achillecalegari/calegari-view-2/docs/img/02_front.jpg

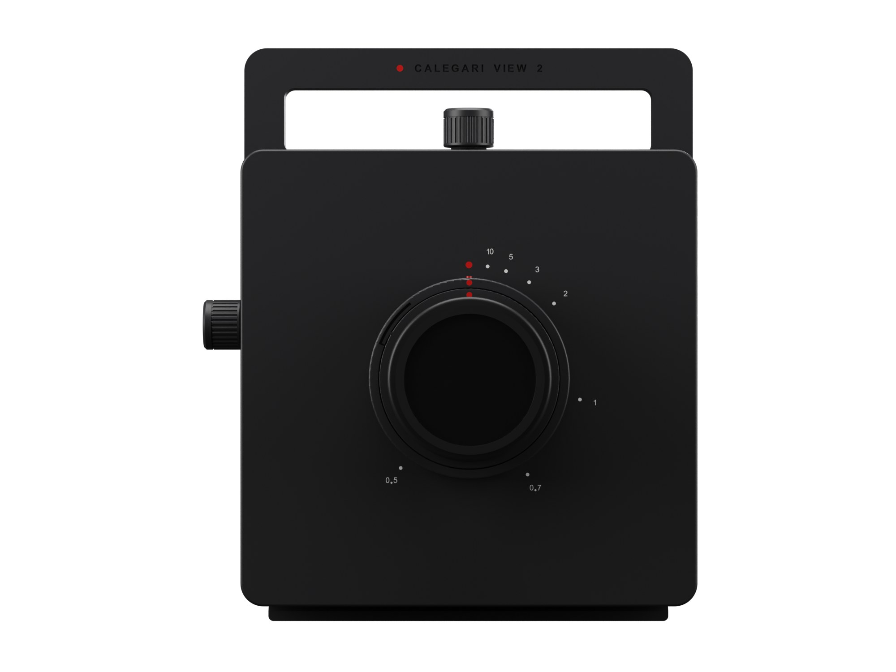
docs/img/02_front.jpg
