achillecalegari/calegari-view-2/docs/img/05_top.jpg

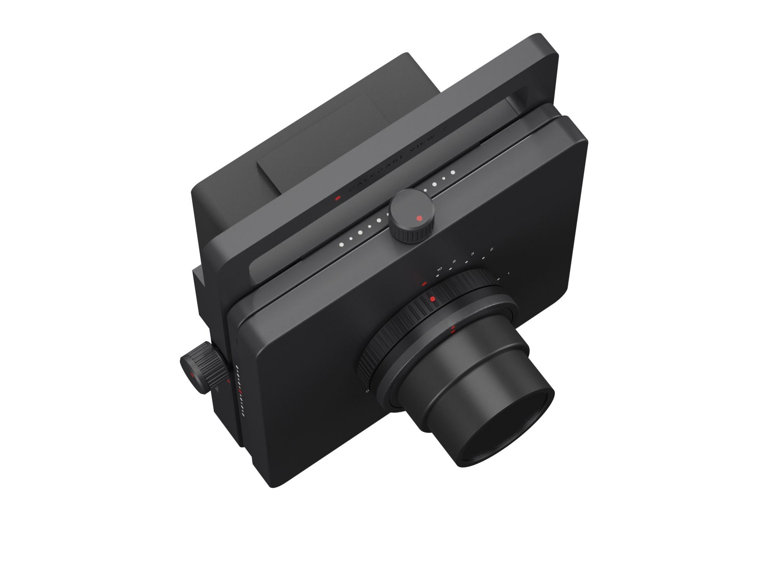
docs/img/05_top.jpg
