achillecalegari/calegari-view-2/print/plates/plate_00d_test_tpu.3mf

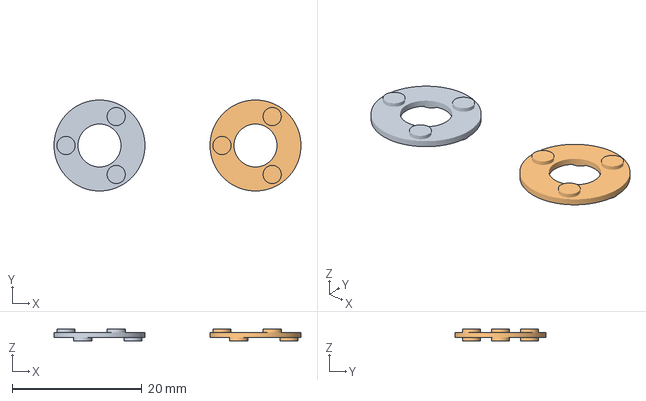
[picture p22: CAD file, 2026-09-29]
print/plates/plate_00d_test_tpu.3mf
38.0 x 14.0 x 1.80 mm
tpu_drag_washer
tpu_drag_washer_b
