achillecalegari/calegari-view-2/print/step/plug_x_bottom.step

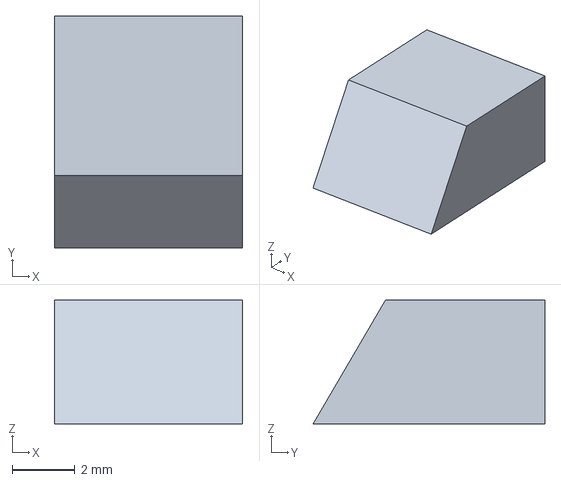
[picture p23: CAD file, 2026-09-29]
print/step/plug_x_bottom.step
6.01 x 7.41 x 3.95 mm
