achillecalegari/calegari-view-2/print/test/worm_rig_plug.stl

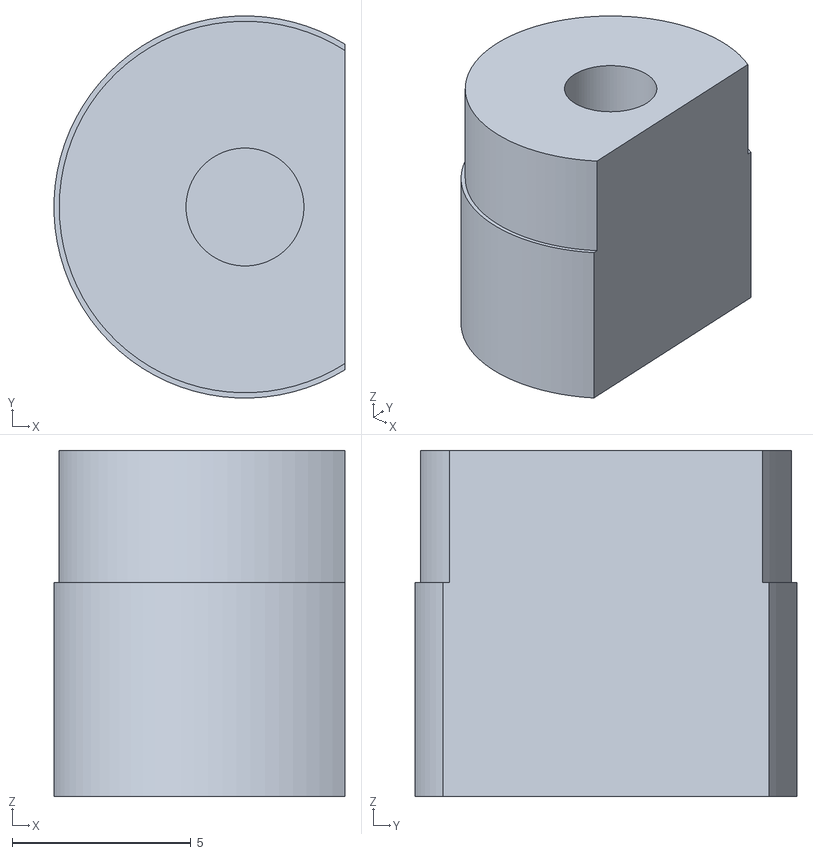
[picture p24: CAD file, 2026-09-28]
print/test/worm_rig_plug.stl
8.15 x 10.7 x 9.70
