achillecalegari/calegari-view-2/print/plates/plate_00c_test_ways_arca.3mf

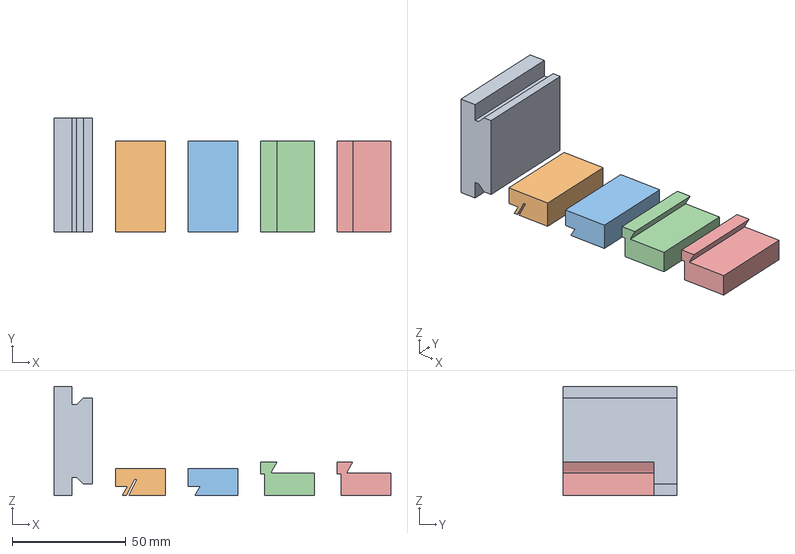
[picture p25: CAD file, 2026-09-29]
print/plates/plate_00c_test_ways_arca.3mf
148.4 x 50.0 x 48.0 mm
arca_coupon
way_groove_flexure
way_groove_rigid
way_tongue_flexure
way_tongue_rigid
