achillecalegari/calegari-view-2/print/test/collar.stl

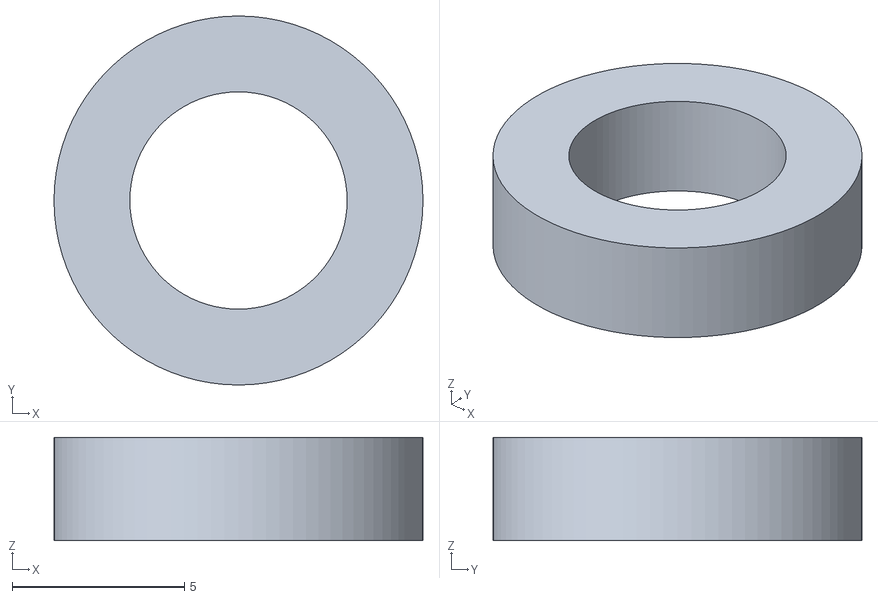
[picture p26: CAD file, 2026-09-28]
print/test/collar.stl
10.7 x 10.7 x 3.00
