achillecalegari/calegari-view-2/print/plates/plate_04_black_0.12mm_layers.3mf

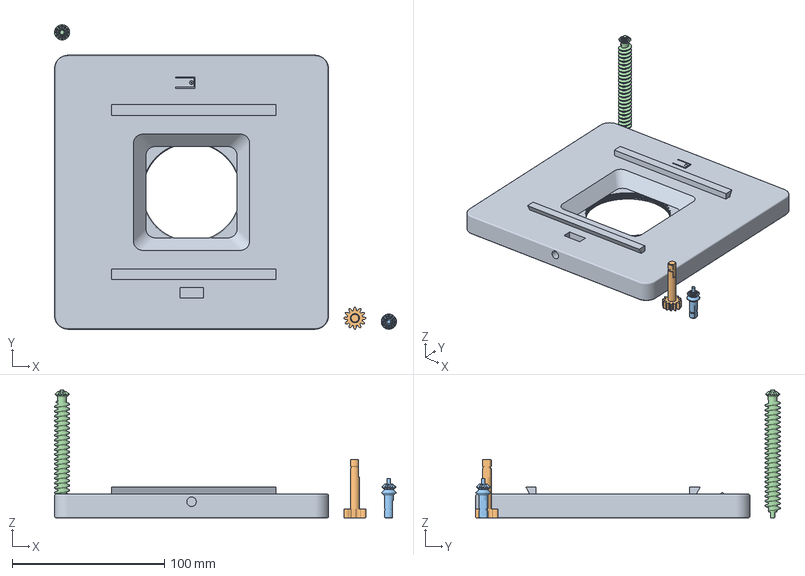
[picture p27: CAD file, 2026-09-29]
print/plates/plate_04_black_0.12mm_layers.3mf
224.6 x 200.0 x 83.9 mm
lens_panel
pinion_shift
rise_knob_gear
rise_worm
