achillecalegari/calegari-view-2/print/step/plug_worm.step

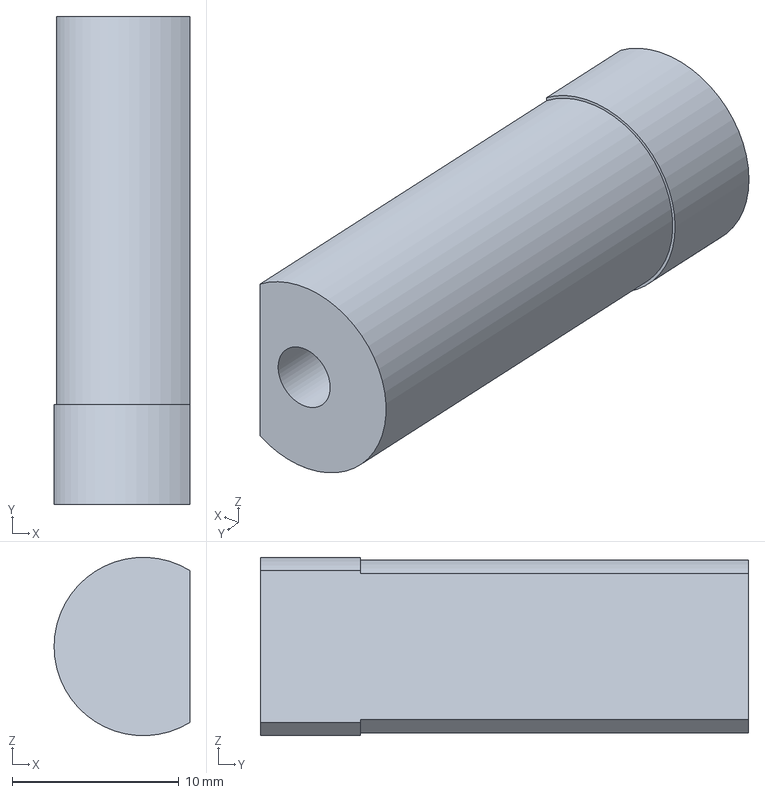
[picture p28: CAD file, 2026-09-29]
print/step/plug_worm.step
8.15 x 29.3 x 10.7 mm
