achillecalegari/calegari-view-2/print/test/pinion_shaft.stl

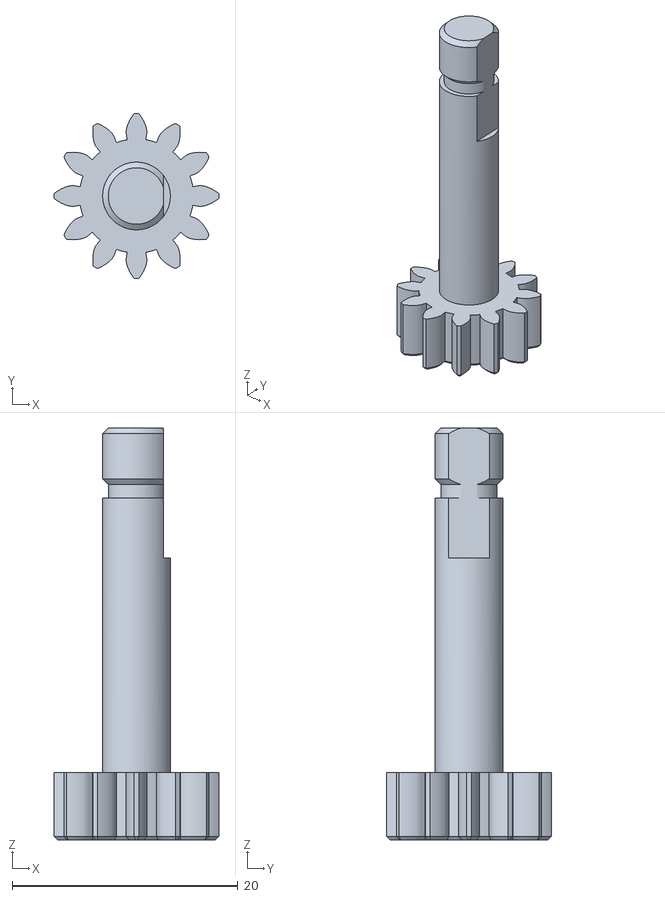
[picture p29: CAD file, 2026-09-28]
print/test/pinion_shaft.stl
14.6 x 14.6 x 36.5
