achillecalegari/calegari-view-2/print/plates/plate_02_black.3mf

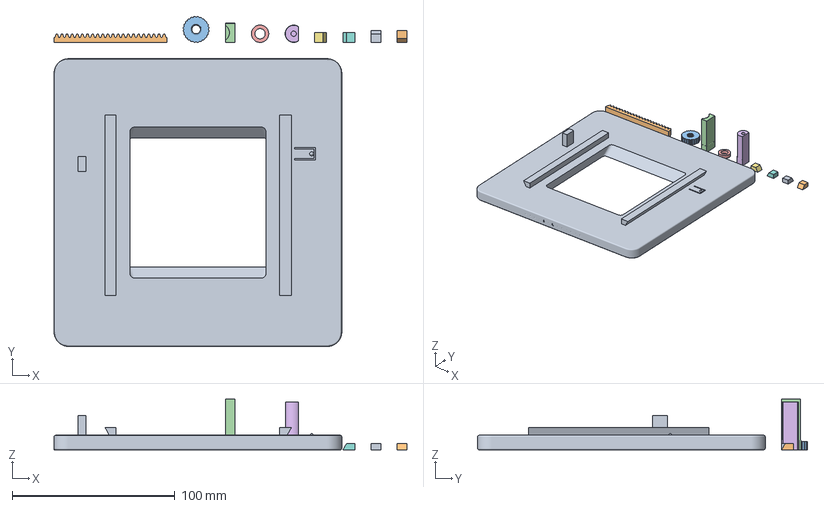
[picture p30: CAD file, 2026-09-29]
print/plates/plate_02_black.3mf
217.1 x 203.0 x 31.2 mm
y_plate
rack_shift
graflok_wheel
plug_rack
rise_collar
plug_worm
plug_y_left
plug_y_right
plug_x_top
plug_x_bottom
