achillecalegari/calegari-view-2/print/step/y_plate.step

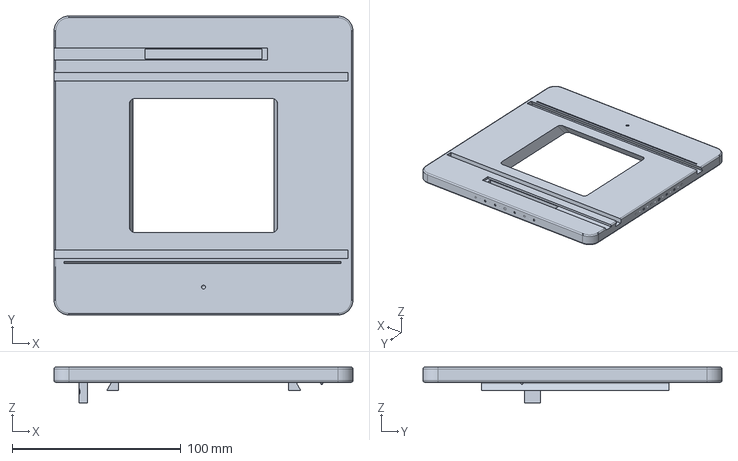
[picture p31: CAD file, 2026-09-29]
print/step/y_plate.step
177.0 x 177.0 x 21.2 mm
