achillecalegari/calegari-view-2/print/step/graflok_wheel.step

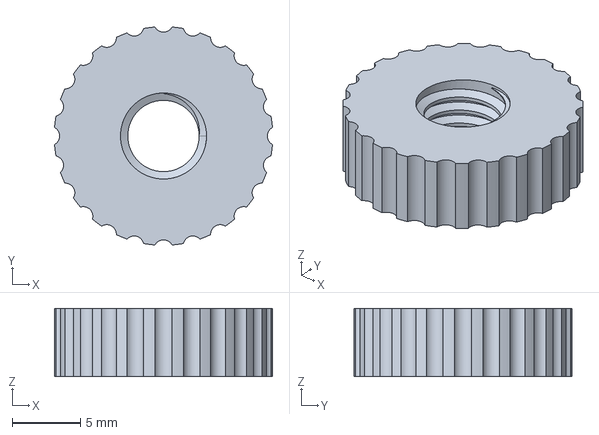
[picture p32: CAD file, 2026-09-29]
print/step/graflok_wheel.step
16.0 x 16.0 x 5.00 mm
