achillecalegari/calegari-view-2/print/test/rack_62.stl

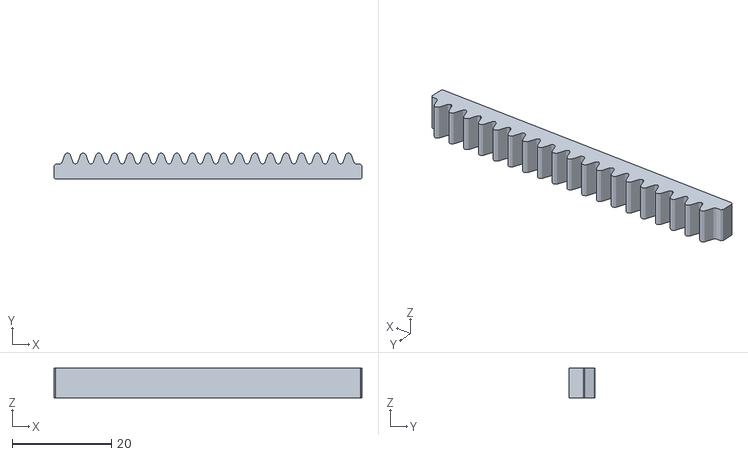
[picture p33: CAD file, 2026-09-28]
print/test/rack_62.stl
62.0 x 5.25 x 6.00
