achillecalegari/calegari-view-2/print/plates/plate_00b_test_lens_drive.3mf

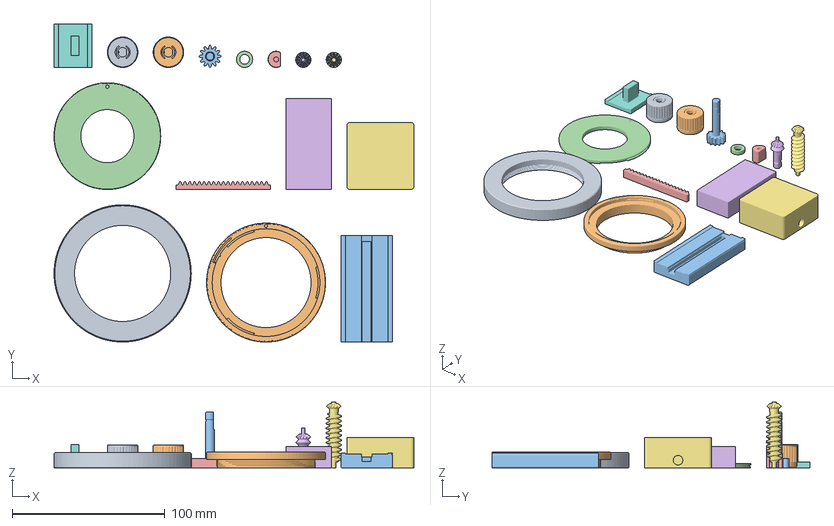
[picture p34: CAD file, 2026-09-29]
print/plates/plate_00b_test_lens_drive.3mf
236.0 x 208.6 x 43.1 mm
thread_coupon_M65_female
lens_mount
rack_carrier
lens_board
rack_62
worm_block
pinion_block
rise_rack_slice
knob
knob_b
pinion_shaft
collar
worm_rig_plug
knob_gear
worm_short
