achillecalegari/calegari-view-2/print/step/lens_panel.step

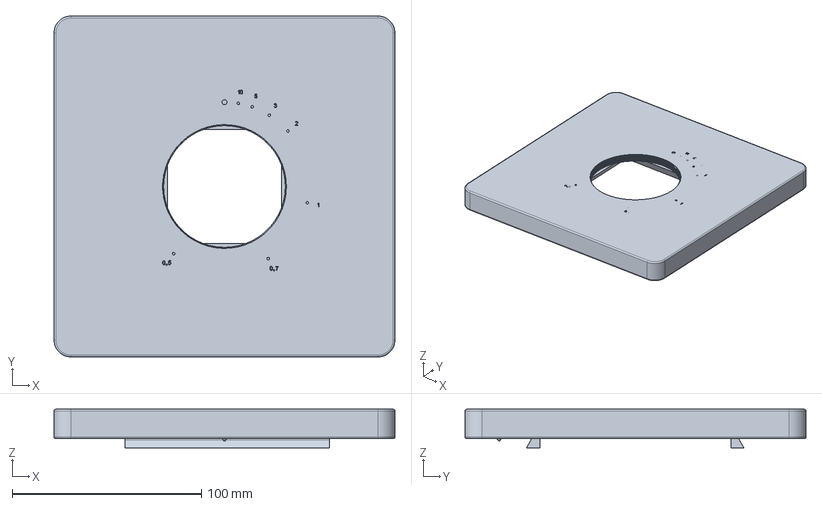
[picture p35: CAD file, 2026-09-29]
print/step/lens_panel.step
180.0 x 180.0 x 20.4 mm
