achillecalegari/calegari-view-2/print/test/thread_coupon_M65_female.stl

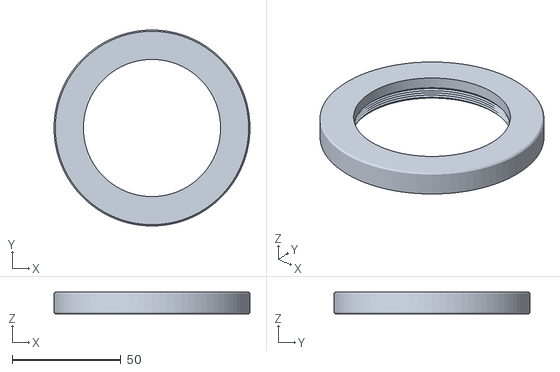
[picture p36: CAD file, 2026-09-28]
print/test/thread_coupon_M65_female.stl
90.0 x 90.0 x 10.0
