achillecalegari/calegari-view-2/print/test/arca_coupon.stl

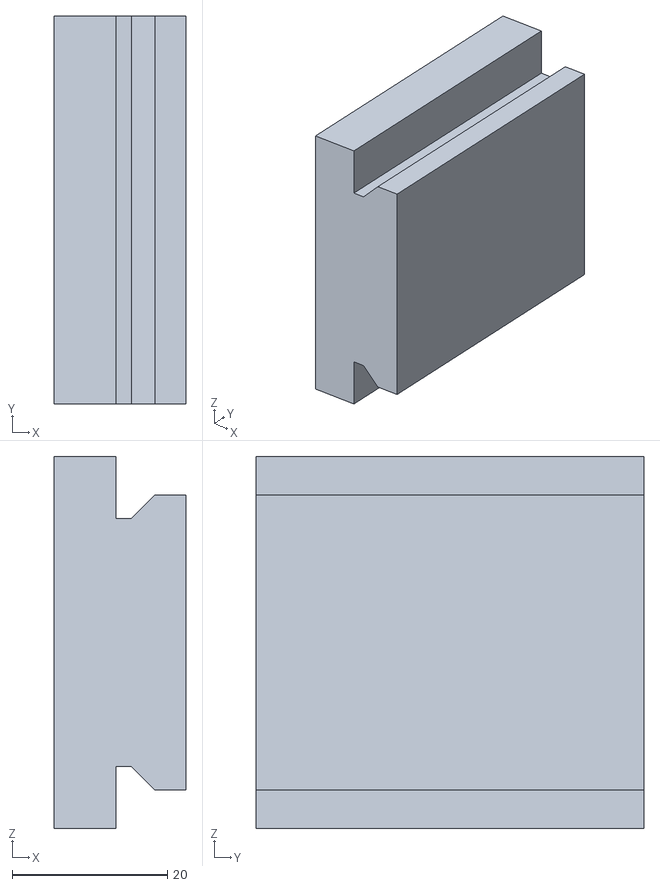
[picture p37: CAD file, 2026-09-28]
print/test/arca_coupon.stl
17.0 x 50.0 x 48.0
