achillecalegari/calegari-view-2/print/test/way_tongue_rigid.stl

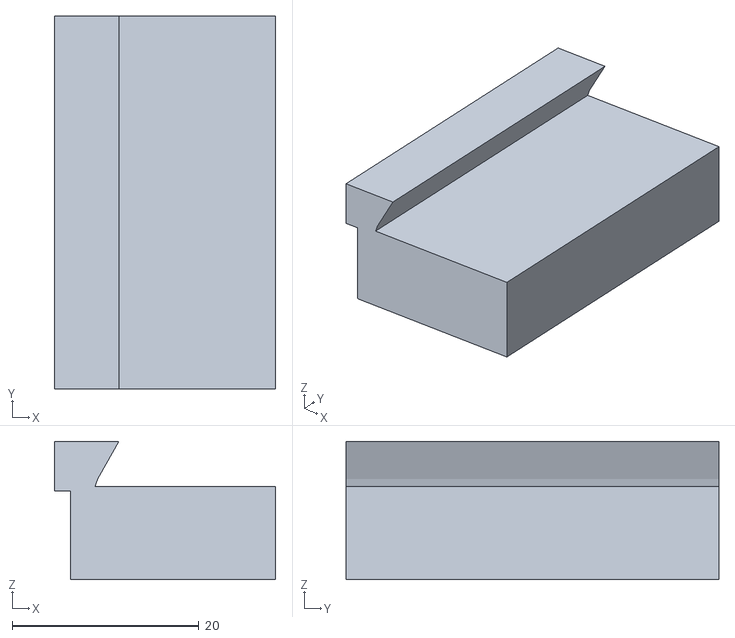
[picture p38: CAD file, 2026-09-28]
print/test/way_tongue_rigid.stl
23.7 x 40.0 x 14.8
