achillecalegari/calegari-view-2/print/step/pinion_shift.step

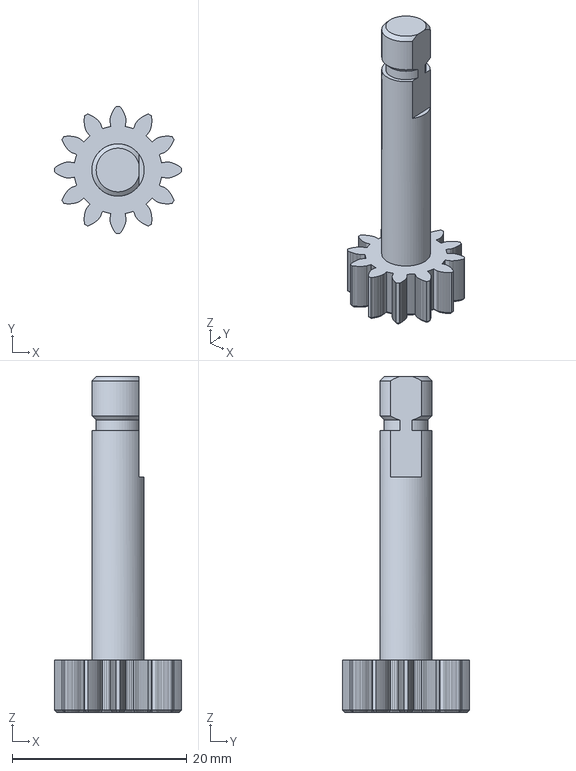
[picture p39: CAD file, 2026-09-29]
print/step/pinion_shift.step
14.6 x 14.6 x 38.5 mm
