achillecalegari/calegari-view-2/print/step/rise_worm.step

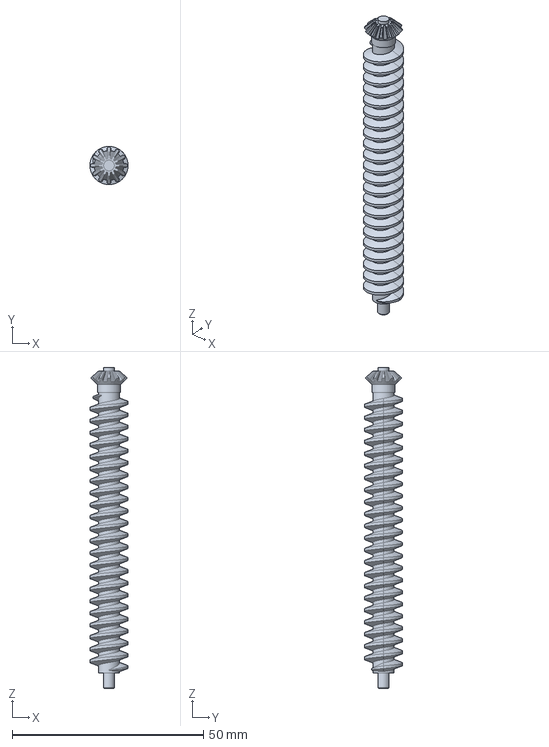
[picture p40: CAD file, 2026-09-29]
print/step/rise_worm.step
10.00 x 10.00 x 83.9 mm
