achillecalegari/calegari-view-2/print/test/way_groove_flexure.stl

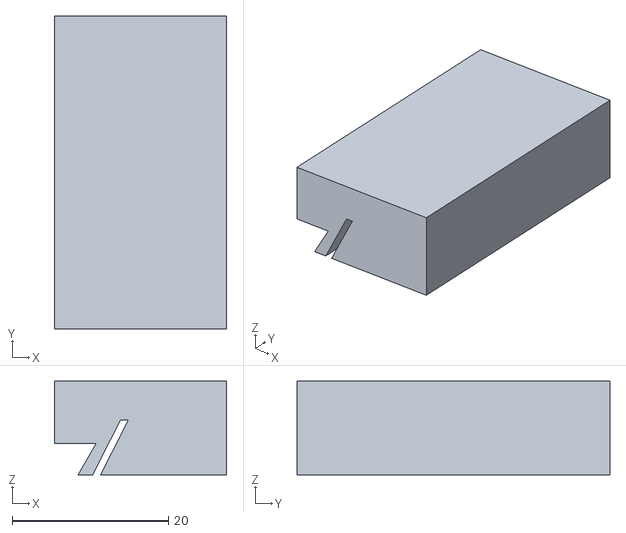
[picture p41: CAD file, 2026-09-28]
print/test/way_groove_flexure.stl
22.0 x 40.0 x 12.0
