achillecalegari/calegari-view-2/print/step/plug_rack.step

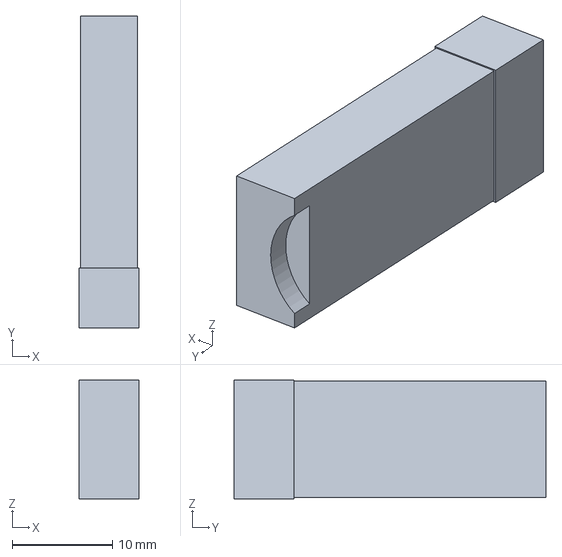
[picture p42: CAD file, 2026-09-29]
print/step/plug_rack.step
6.00 x 31.2 x 11.8 mm
