achillecalegari/calegari-view-2/print/step/stop_peg.step

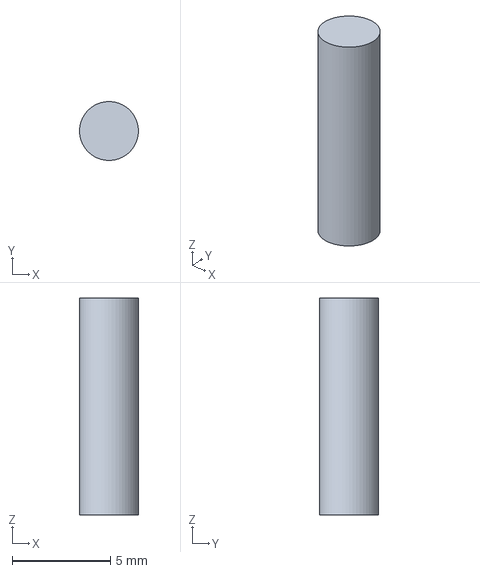
[picture p43: CAD file, 2026-09-29]
print/step/stop_peg.step
3.00 x 3.00 x 11.1 mm
