achillecalegari/calegari-view-2/print/step/rotator.step

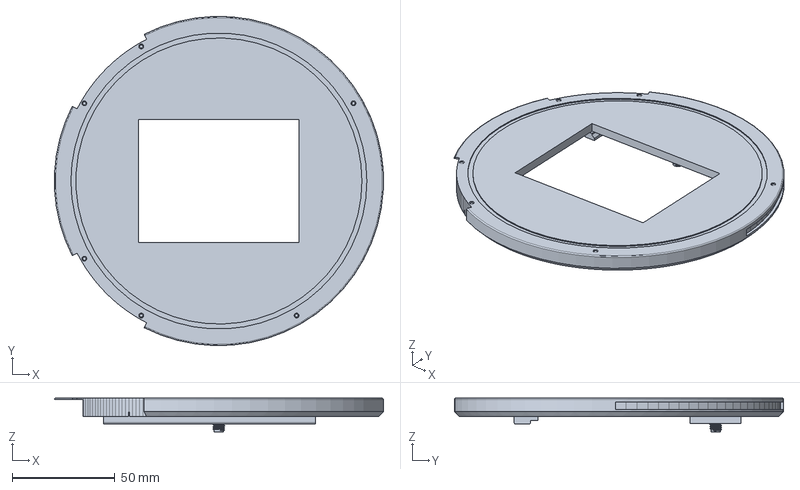
[picture p44: CAD file, 2026-09-29]
print/step/rotator.step
159.9 x 160.0 x 16.4 mm
