achillecalegari/calegari-view-2/print/test/way_groove_rigid.stl

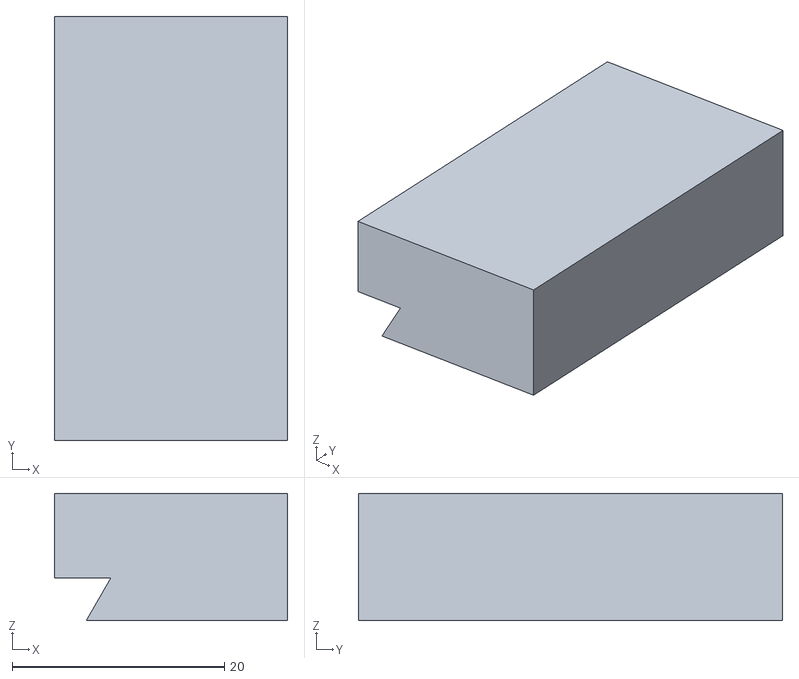
[picture p45: CAD file, 2026-09-28]
print/test/way_groove_rigid.stl
22.0 x 40.0 x 12.0
