achillecalegari/calegari-view-2/print/test/pinion_block.stl

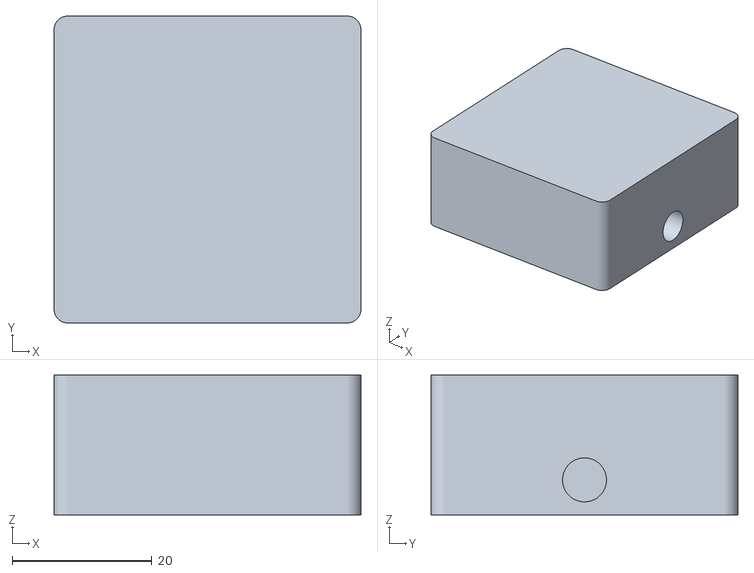
[picture p46: CAD file, 2026-09-28]
print/test/pinion_block.stl
44.0 x 44.0 x 20.0
